hostaboat/crab_timer/teensy32/vs1053_plugins.cpp

#include "vs1053_plugins.h"
#include <cstdint>

// In addition to the patches here, there are also a bunch of plugins at:
// http://www.vlsi.fi/en/support/software/vs10xxplugins.html

// http://www.vlsi.fi/fileadmin/software/VS10XX/vs1053b-patches.pdf

// There are some known problems in the VS1053b firmware that this
// patch addresses.
// * Vorbis: Occasional windowing overflow.
// * Vorbis: Ogg streams that have the highest bit set in stream serial number
//           are not played.
// * Vorbis: Ogg streams that have larger than 32-bit sample position will skip
//           some samples every 232 samples (27 hours at 44.1 kHz).
// * Vorbis: If the first four bytes of Ogg Vorbis file wrap from the end of
//           the stream buffer to the beginning, the decoding will get stuck.
// * Vorbis: If left channel is empty (digital 0), right channel may be ignored.
// * AAC: MP4 format with unused data at the start of the mdat atom are not played.
// * AAC: HE-AAC: PS header frame must be present in the first encountered SBR
//        frame when PS is present or the decoding may crash.
// * AAC: Automatic clock change and feature drop is too forgiving.
// * MP2: Invalid MPEG header can cause a lockup.
// * IMA ADPCM encoding does not send encoded data.
// * SS_REFERENCE_SEL is cleared by firmware so the higher 1.65V reference
//   voltage can not be permanently activated.
// * SS_DO_NOT_JUMP is not by default cleared at software reset.
// * MP3: mp3 decoder in vs1053b does not calculate the amount of valid data in
//        bit reservoir, so if you start decoding in a middle of an mp3 stream,
//        decoding can access invalid data and cause audible disturbances.
// * Samplerate is changed immediately although audio buffer can still contain
//   data with the old samplerate.
// * AAC: Automatic feature drop does not work with non-implicit upsample mode.
// * AAC: PNS of left channel can be corrupted in transition frames.
// * AAC: ADTS decoding ignored the crc flag.
// * AAC: MP4 header decoding did not StreamDiscard() at the correct point.
// * AAC: MP4 header decoding sometimes assumed an atom had subatoms when it did not.
// * AAC: Added a simplified LATM/LOAS parser for DAB+ use.
// * Resampler: to be able to use rate tune with 48kHz and 12.288MHz XTALI.
// * ID3v2 can contain data that matches a decodable format. An ID3 parser now
//   skips the extra data correctly.
//
// When the patch is loaded, it starts automatically (writes 0x0300 to AIADDR)
// and restarts the system (you should wait for DREQ to rise). The patch must
// be re-loaded after each hardware or software reset. If you replace software
// reset by writing 0x0300 to AIADDR, you do not need to reload the patch.

#if defined VS1053B_PATCHES_PLUGIN
const uint16_t vs1053b_patches_plugin[] = {
	0x0007,0x0001, // copy 1
	0x8050,
	0x0006,0x0002, // copy 2
	0x2a00,0xc000,
	0x0006, 0x801e, 0x0000, // Rle(30)
	0x0006,0x0488, // copy 1160
	0xf400,0x4095,0x0000,0x02c2,0x6124,0x0024,0x0000,0x0024,
	0x2800,0x1ac5,0x4192,0x4542,0x0000,0x0041,0x2000,0x0015,
	0x0030,0x0317,0x2000,0x0000,0x3f00,0x4024,0x2000,0x0000,
	0x0000,0x0000,0x3e12,0x3800,0x3e00,0xb804,0x0030,0x0015,
	0x0007,0x8257,0x3700,0x984c,0xf224,0x1444,0xf224,0x0024,
	0x0008,0x0002,0x2910,0x0181,0x0000,0x1bc8,0xb428,0x1402,
	0x0000,0x8004,0x2910,0x0195,0x0000,0x1bc8,0xb428,0x0024,
	0x0006,0x0095,0x2800,0x2945,0x3e13,0x780e,0x3e11,0x7803,
	0x3e13,0xf806,0x3e11,0xf801,0x3510,0xb808,0x003f,0xe004,
	0xfec4,0x3800,0x48be,0x17c3,0xfe46,0x41c2,0x48be,0x4497,
	0x4090,0x1c46,0xf06c,0x0024,0x2400,0x2580,0x6090,0x41c3,
	0x6628,0x1c47,0x0000,0x0024,0x2800,0x2449,0xf07e,0x0024,
	0xf400,0x4182,0x673a,0x1c46,0x0000,0x0024,0x2800,0x2589,
	0xf06c,0x0024,0xf400,0x41c3,0x0000,0x0024,0x4224,0x3442,
	0x2900,0xa200,0x4336,0x37c3,0x0000,0x1805,0x2900,0xa200,
	0x4508,0x40c2,0x450a,0x9808,0x0000,0x0207,0xa478,0x1bc0,
	0xc45a,0x1807,0x0030,0x03d5,0x3d01,0x5bc1,0x36f3,0xd806,
	0x3601,0x5803,0x36f3,0x0024,0x36f3,0x580e,0x0007,0x8257,
	0x0000,0x6004,0x3730,0x8024,0xb244,0x1c04,0xd428,0x3c02,
	0x0006,0xc717,0x2800,0x2d05,0x4284,0x0024,0x3613,0x3c02,
	0x0006,0xc357,0x2901,0x6600,0x3e11,0x5c05,0x4284,0x1bc5,
	0x0000,0x0024,0x2800,0x2fc5,0x0000,0x0024,0x3613,0x0024,
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
	0x0001,
	0x0006, 0x8007, 0x0000, // Rle(7)
	0x0006,0x0018, // copy 24
	0x0002,0x0000,0xffff,0xffff,0x0000,0x0000,0x0000,0x0000,
	0x0003,0x0000,0xfffd,0xffff,0x0001,0x0000,0x0000,0x0000,
	0x0004,0x0000,0xfffa,0xffff,0x0004,0x0000,0xffff,0xffff,
	0x000a,0x0001, // copy 1
	0x0300
};
#endif
