hostaboat/crab_timer/spi_util.cpp

#include <cstdint>
#include <kinetis.h>
#include "spi_util.h"

#ifndef F_BUS
# error "F_BUS not defined"
#endif

////////////////////////////////////////////////////////////////////////////////
// Clock and Transfer Attributes
// uint32_t sck   - frequency in Hz
// uint32_t t_csc - the delay between assertion of PCS and the first edge of SCK
// uint32_t t_asc - the delay between the last edge of SCK and negation of PCS
// uint32_t t_dt  - the time between negation of PCS and next assertion of PCS
// This function returns the relevant bits for use in the CTAR field.
uint32_t CTAR(uint32_t sck, uint32_t t_csc, uint32_t t_asc, uint32_t t_dt)
{
    return (CTAR_sck(sck)
            | CTAR_pcs_to_sck_delay(t_csc)
            | CTAR_delay_after_sck(t_asc)
            | CTAR_delay_after_transfer(t_dt));
}

////////////////////////////////////////////////////////////////////////////////
// SCK baud rate to be used for SPI transfers.
// Given the frequency in Hz argument passed in, this function
// returns the relevant bits for use in the CTAR field.
uint32_t CTAR_sck(uint32_t frequency)
{
    uint32_t sck;

#if F_BUS == 60000000
    if (frequency >= 30000000)
        sck = (SPI_CTAR_BR(0) | SPI_CTAR_PBR(0) | SPI_CTAR_DBR);
    else if (frequency >= 15000000)
        sck = (SPI_CTAR_BR(0) | SPI_CTAR_PBR(0));
    else if (frequency >= 10000000)
        sck = (SPI_CTAR_BR(0) | SPI_CTAR_PBR(1));
    else if (frequency >= 7500000)
        sck = (SPI_CTAR_BR(1) | SPI_CTAR_PBR(0));
    else if (frequency >= 6000000)
        sck = (SPI_CTAR_BR(0) | SPI_CTAR_PBR(2));
    else if (frequency >= 5000000)
        sck = (SPI_CTAR_BR(1) | SPI_CTAR_PBR(1));
    else if (frequency >= 4285714)
        sck = (SPI_CTAR_BR(0) | SPI_CTAR_PBR(3));
    else if (frequency >= 3750000)
        sck = (SPI_CTAR_BR(3) | SPI_CTAR_PBR(0));
    else if (frequency >= 3333333)
        sck = (SPI_CTAR_BR(2) | SPI_CTAR_PBR(1));
    else if (frequency >= 3000000)
        sck = (SPI_CTAR_BR(1) | SPI_CTAR_PBR(2));
    else if (frequency >= 2500000)
        sck = (SPI_CTAR_BR(3) | SPI_CTAR_PBR(1));
    else if (frequency >= 2142857)
        sck = (SPI_CTAR_BR(1) | SPI_CTAR_PBR(3));
    else if (frequency >= 2000000)
        sck = (SPI_CTAR_BR(2) | SPI_CTAR_PBR(2));
    else if (frequency >= 1875000)
        sck = (SPI_CTAR_BR(4) | SPI_CTAR_PBR(0));
    else if (frequency >= 1500000)
        sck = (SPI_CTAR_BR(3) | SPI_CTAR_PBR(2));
    else if (frequency >= 1428571)
        sck = (SPI_CTAR_BR(2) | SPI_CTAR_PBR(3));
    else if (frequency >= 1250000)
        sck = (SPI_CTAR_BR(4) | SPI_CTAR_PBR(1));
    else if (frequency >= 1071428)
        sck = (SPI_CTAR_BR(3) | SPI_CTAR_PBR(3));
    else if (frequency >= 937500)
        sck = (SPI_CTAR_BR(5) | SPI_CTAR_PBR(0));
    else if (frequency >= 750000)
        sck = (SPI_CTAR_BR(4) | SPI_CTAR_PBR(2));
    else if (frequency >= 625000)
        sck = (SPI_CTAR_BR(5) | SPI_CTAR_PBR(1));
    else if (frequency >= 535714)
        sck = (SPI_CTAR_BR(4) | SPI_CTAR_PBR(3));
    else if (frequency >= 468750)
        sck = (SPI_CTAR_BR(6) | SPI_CTAR_PBR(0));
    else if (frequency >= 375000)
        sck = (SPI_CTAR_BR(5) | SPI_CTAR_PBR(2));
    else if (frequency >= 312500)
        sck = (SPI_CTAR_BR(6) | SPI_CTAR_PBR(1));
    else if (frequency >= 267857)
        sck = (SPI_CTAR_BR(5) | SPI_CTAR_PBR(3));
    else if (frequency >= 234375)
        sck = (SPI_CTAR_BR(7) | SPI_CTAR_PBR(0));
    else if (frequency >= 187500)
        sck = (SPI_CTAR_BR(6) | SPI_CTAR_PBR(2));
    else if (frequency >= 156250)
        sck = (SPI_CTAR_BR(7) | SPI_CTAR_PBR(1));
    else if (frequency >= 133928)
        sck = (SPI_CTAR_BR(6) | SPI_CTAR_PBR(3));
    else if (frequency >= 117187)
        sck = (SPI_CTAR_BR(8) | SPI_CTAR_PBR(0));
    else if (frequency >= 93750)
        sck = (SPI_CTAR_BR(7) | SPI_CTAR_PBR(2));
    else if (frequency >= 78125)
        sck = (SPI_CTAR_BR(8) | SPI_CTAR_PBR(1));
    else if (frequency >= 66964)
        sck = (SPI_CTAR_BR(7) | SPI_CTAR_PBR(3));
    else if (frequency >= 58593)
        sck = (SPI_CTAR_BR(9) | SPI_CTAR_PBR(0));
    else if (frequency >= 46875)
        sck = (SPI_CTAR_BR(8) | SPI_CTAR_PBR(2));
    else if (frequency >= 39062)
        sck = (SPI_CTAR_BR(9) | SPI_CTAR_PBR(1));
    else if (frequency >= 33482)
        sck = (SPI_CTAR_BR(8) | SPI_CTAR_PBR(3));
    else if (frequency >= 29296)
        sck = (SPI_CTAR_BR(10) | SPI_CTAR_PBR(0));
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
        t_csc = (SPI_CTAR_CSSCK(12) | SPI_CTAR_PCSSCK(0));
    else if (nanoseconds <= 5120000)
        t_csc = (SPI_CTAR_CSSCK(10) | SPI_CTAR_PCSSCK(2));
    else if (nanoseconds <= 6144000)
        t_csc = (SPI_CTAR_CSSCK(11) | SPI_CTAR_PCSSCK(1));
    else if (nanoseconds <= 7168000)
        t_csc = (SPI_CTAR_CSSCK(10) | SPI_CTAR_PCSSCK(3));
    else if (nanoseconds <= 8192000)
        t_csc = (SPI_CTAR_CSSCK(13) | SPI_CTAR_PCSSCK(0));
    else if (nanoseconds <= 10240000)
        t_csc = (SPI_CTAR_CSSCK(11) | SPI_CTAR_PCSSCK(2));
    else if (nanoseconds <= 12288000)
        t_csc = (SPI_CTAR_CSSCK(12) | SPI_CTAR_PCSSCK(1));
    else if (nanoseconds <= 14336000)
        t_csc = (SPI_CTAR_CSSCK(11) | SPI_CTAR_PCSSCK(3));
    else if (nanoseconds <= 16384000)
        t_csc = (SPI_CTAR_CSSCK(14) | SPI_CTAR_PCSSCK(0));
    else if (nanoseconds <= 20480000)
        t_csc = (SPI_CTAR_CSSCK(12) | SPI_CTAR_PCSSCK(2));
    else if (nanoseconds <= 24576000)
        t_csc = (SPI_CTAR_CSSCK(13) | SPI_CTAR_PCSSCK(1));
    else if (nanoseconds <= 28672000)
        t_csc = (SPI_CTAR_CSSCK(12) | SPI_CTAR_PCSSCK(3));
    else if (nanoseconds <= 32768000)
        t_csc = (SPI_CTAR_CSSCK(15) | SPI_CTAR_PCSSCK(0));
    else if (nanoseconds <= 40960000)
        t_csc = (SPI_CTAR_CSSCK(13) | SPI_CTAR_PCSSCK(2));
    else if (nanoseconds <= 49152000)
        t_csc = (SPI_CTAR_CSSCK(14) | SPI_CTAR_PCSSCK(1));
    else if (nanoseconds <= 57344000)
        t_csc = (SPI_CTAR_CSSCK(13) | SPI_CTAR_PCSSCK(3));
    else if (nanoseconds <= 81920000)
        t_csc = (SPI_CTAR_CSSCK(14) | SPI_CTAR_PCSSCK(2));
    else if (nanoseconds <= 98304000)
        t_csc = (SPI_CTAR_CSSCK(15) | SPI_CTAR_PCSSCK(1));
    else if (nanoseconds <= 114688000)
        t_csc = (SPI_CTAR_CSSCK(14) | SPI_CTAR_PCSSCK(3));
    else if (nanoseconds <= 163840000)
        t_csc = (SPI_CTAR_CSSCK(15) | SPI_CTAR_PCSSCK(2));
    else
        t_csc = (SPI_CTAR_CSSCK(15) | SPI_CTAR_PCSSCK(3));
#else
# error "F_BUS not valid"
#endif

    return t_csc;
}

////////////////////////////////////////////////////////////////////////////////
// This is the delay between the last edge of SCK and the negation of PCS.
// Given the nanosecond Delay After SCK argument passed in, this
// function returns the relevant bits for use in the CTAR field.
uint32_t CTAR_delay_after_sck(uint32_t nanoseconds)
{
    uint32_t t_asc;
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
